volkangokyar01/deck-app/case/v6/v6_ekran_tutucu.png

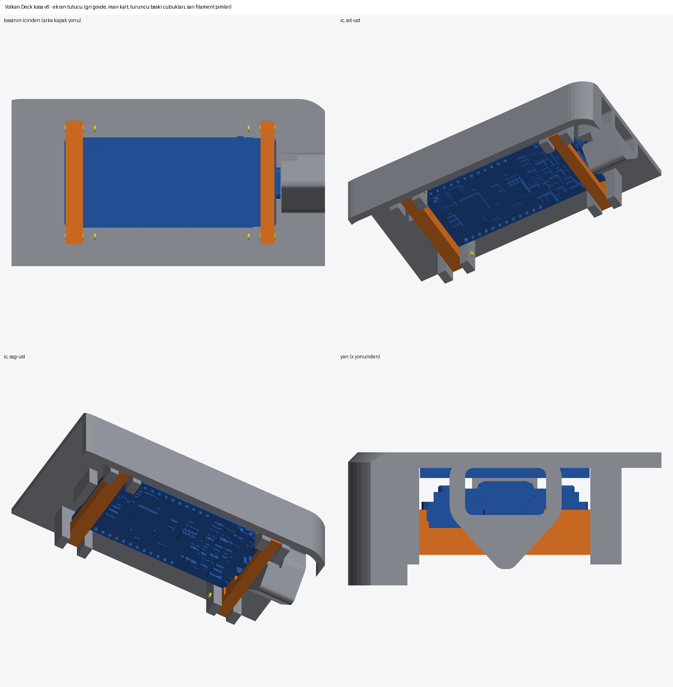
case/v6/v6_ekran_tutucu.png
