volkangokyar01/deck-app/case/v6/v6_usb_ayak.png

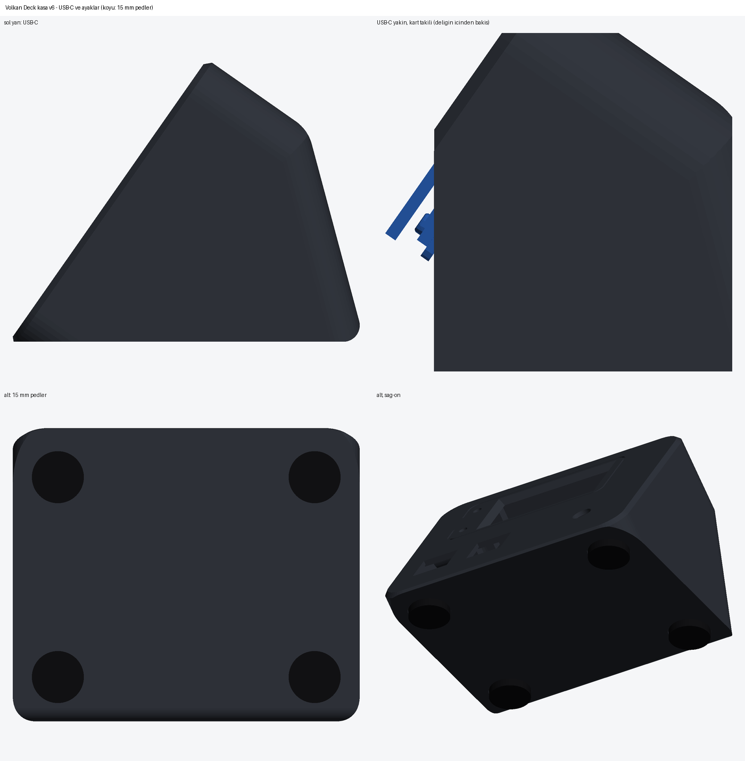
case/v6/v6_usb_ayak.png
