volkangokyar01/deck-app/case/v6/v6_usb_kesit.png

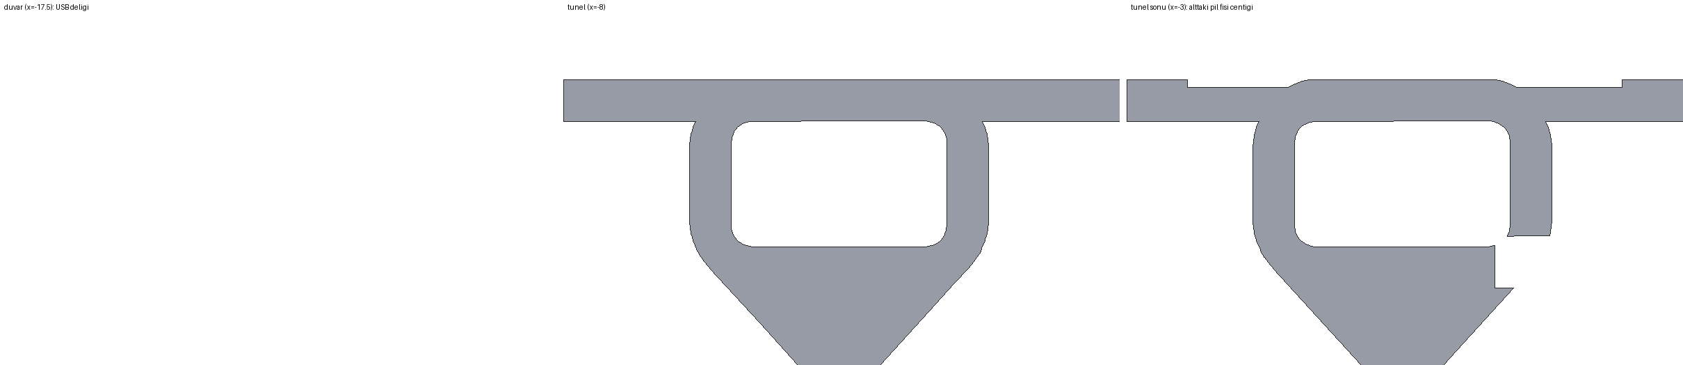
case/v6/v6_usb_kesit.png
