volkangokyar01/deck-app/firmware/VolkanDeck/Proto.h

#pragma once
#include "esp_psram.h"
#include "esp_efuse.h"
#include "esp_efuse_table.h"
#include "mbedtls/base64.h"
#include "esp32-hal-tinyusb.h"

static const size_t LINEBUF_MAX = 128 * 1024;

// Crash breadcrumbs: survive a panic / watchdog reset, reported once in the hello reply ("crash")
RTC_NOINIT_ATTR static uint32_t crumbMagic;
RTC_NOINIT_ATTR static char crumbWhere[28];
static const uint32_t CRUMB_MAGIC = 0x56444352;
static String bootReset, bootCrash;
static void crumbSet(const char* a, const char* b = "") {
  size_t i = 0;
  for (const char* s = a; *s && i < sizeof(crumbWhere) - 1; ) crumbWhere[i++] = *s++;
  if (*b && i < sizeof(crumbWhere) - 1) crumbWhere[i++] = ':';
  for (const char* s = b; *s && i < sizeof(crumbWhere) - 1; ) crumbWhere[i++] = *s++;
  crumbWhere[i] = 0; crumbMagic = CRUMB_MAGIC;
}
static void crumbClear() { crumbMagic = 0; }
static void crumbBoot() {
  esp_reset_reason_t r = esp_reset_reason();
  const char* n = r == ESP_RST_POWERON ? "poweron" : r == ESP_RST_SW ? "software" : r == ESP_RST_PANIC ? "panic" : r == ESP_RST_INT_WDT ? "int_wdt"
                : r == ESP_RST_TASK_WDT ? "task_wdt" : r == ESP_RST_WDT ? "wdt" : r == ESP_RST_BROWNOUT ? "brownout" : r == ESP_RST_DEEPSLEEP ? "deepsleep" : "other";
  bootReset = n;
  bool bad = r == ESP_RST_PANIC || r == ESP_RST_INT_WDT || r == ESP_RST_TASK_WDT || r == ESP_RST_WDT || r == ESP_RST_BROWNOUT;
  crumbWhere[sizeof(crumbWhere) - 1] = 0;
  if (bad) bootCrash = String(n) + (crumbMagic == CRUMB_MAGIC ? String(" @ ") + crumbWhere : String(""));
  crumbMagic = 0;
}
static void ecoSuspend();
static uint32_t transferAt = 0;
static volatile bool usbPartial = false;
static File animUp; static size_t animBytes = 0, animGot = 0; static int animW = 0, animH = 0, animN = 0, animFpsIn = 15; static bool animUpLight = false;
bool configChangedFlag = false;
uint32_t rxBytes = 0, rxLines = 0;
static void* bigAlloc(size_t n) { void* p = psramOk() ? ps_malloc(n) : nullptr; if (!p) p = malloc(n); return p; }      // main applies side effects
String pendingName;
uint32_t companionAt = 0; bool companionNew = false, companionMediaLaunch = false;
bool mediaDirty = false; uint32_t sysLocalAt = 0;
bool mailNew = false;

// Two transports carry the same JSON lines: USB serial and the Bluetooth data channel (Hid.h).
// Replies go back where the command came from; events go to the desktop app's link (USB first).
enum Src : uint8_t { SRC_USB = 0, SRC_BLE };
uint32_t companionUsbAt = 0, companionBleAt = 0;
static int8_t replySrc = -1;                         // set while a command is handled
static bool bleHostOn() { return bleHostConn != BLE_HS_CONN_HANDLE_NONE; }
static bool usbCompanion() { return companionUsbAt && millis() - companionUsbAt < 6000 && Serial; }
static bool bleCompanion() { return companionBleAt && millis() - companionBleAt < 6000 && bleHostOn(); }
static bool companionOn() { return usbCompanion() || bleCompanion(); }
static bool hostListening() { return Serial || bleHostOn(); }   // something may read events
static uint8_t eventSrc() {
  uint16_t act = activeHostConn();               // the computer in use gets the events (1.9.1)
  if (act == HOST_USB && Serial) return SRC_USB;
  if (act != BLE_HS_CONN_HANDLE_NONE && act != HOST_USB) return SRC_BLE;
  return usbCompanion() || (Serial && !bleCompanion()) ? SRC_USB : SRC_BLE;
}
static uint16_t eventConn() {
  uint16_t act = activeHostConn();
  return act != BLE_HS_CONN_HANDLE_NONE && act != HOST_USB ? act : bleHostConn;
}

const char* linkName();

// Bluetooth sending runs on its own task: the main loop (screen, knob) never waits for the radio,
// and the NimBLE host task is never blocked by us, so its buffers keep draining.
// One receive buffer per Bluetooth connection (lines from two computers must never mix)
struct BleLink { volatile uint16_t conn = BLE_HS_CONN_HANDLE_NONE; volatile uint16_t mtu = 23; char* buf = nullptr; size_t have = 0; volatile size_t len = 0; };
static const int BLE_LINKS = 3;
static BleLink bleLinks[BLE_LINKS];
static BleLink* bleLinkOf(uint16_t conn) {
  for (auto& L : bleLinks) if (L.conn == conn) return &L;
  return nullptr;
}
static bool bleConnAlive(uint16_t conn) { return conn != BLE_HS_CONN_HANDLE_NONE && bleLinkOf(conn); }
static uint16_t bleMtuOf(uint16_t conn) { BleLink* L = bleLinkOf(conn); return L ? L->mtu : 23; }
static volatile uint16_t replyConn = BLE_HS_CONN_HANDLE_NONE;   // Bluetooth connection of the command being handled
// wifi_scan waiting for the radio (1.13.6): who asked, so the late reply goes back the same way
struct ScanReq { bool on = false; long id = 0; int8_t src = -1; uint16_t conn = BLE_HS_CONN_HANDLE_NONE; uint32_t at = 0; } scanReq;

struct TxItem { char* p; size_t n; uint16_t conn; };
static QueueHandle_t bleTxQ = nullptr;
static void bleTxTask(void*) {
  TxItem it;
  for (;;) {
    if (xQueueReceive(bleTxQ, &it, portMAX_DELAY) != pdTRUE) continue;
    uint16_t conn = it.conn, mtu = bleMtuOf(conn);
    size_t chunk = mtu > 23 ? min<size_t>(mtu - 3, 244) : 20;
    for (size_t i = 0; i < it.n && bleTx && bleConnAlive(conn); ) {
      size_t k = min(chunk, it.n - i);
      if (bleTx->notify((const uint8_t*)it.p + i, k, conn)) { i += k; continue; }
      int tries = 0;
      while (!bleTx->notify((const uint8_t*)it.p + i, k, conn) && bleConnAlive(conn) && ++tries < 400) vTaskDelay(pdMS_TO_TICKS(5));
      if (tries >= 400) break;                       // link stuck for 2 s: drop the rest of this line
      i += k;
    }
    free(it.p);
  }
}
static void sendJson(JsonDocument& d) {   // replies: always write (host just talked to us)
  uint8_t to = replySrc >= 0 ? replySrc : eventSrc();
  if (to == SRC_USB) { serializeJson(d, Serial); Serial.print('\n'); return; }
  uint16_t conn = replySrc >= 0 ? replyConn : eventConn();
  if (!bleTxQ || !bleConnAlive(conn)) return;
  size_t n = measureJson(d);
  TxItem it; it.p = (char*)bigAlloc(n + 2); if (!it.p) return;
  serializeJson(d, it.p, n + 1); it.p[n] = '\n'; it.n = n + 1; it.conn = conn;
  if (xQueueSend(bleTxQ, &it, 0) != pdTRUE) free(it.p);   // queue full: drop (events are refreshed anyway)
}
static void replyOk(JsonVariantConst id) { JsonDocument r; r["id"] = id; r["ok"] = true; sendJson(r); }
static void replyErr(JsonVariantConst id, const char* e) { JsonDocument r; r["id"] = id; r["ok"] = false; r["error"] = e; sendJson(r); }

static void evtInput(const char* ctl) { if (!hostListening()) return; JsonDocument d; d["evt"] = "input"; d["control"] = ctl; sendJson(d); }
static void evtSelect() {
  if (!hostListening() || items.empty()) return;
  JsonDocument d; d["evt"] = "select";
  // a page opened inside the menu reports its own id (the desktop app feeds media / system pages faster)
  d["app"] = items[sel].kind == K_MENU && subPage ? (subPage == K_MEDIA ? "media" : subPage == K_SYS ? "system" : "connections") : itemId(items[sel]);
  sendJson(d);
}
static void evtStatus() {
  if (!hostListening()) return;
  JsonDocument d; d["evt"] = "status"; d["fw"] = FW_VERSION; d["battery"] = batPct; d["charging"] = charging; d["link"] = linkName();
  d["rx"] = rxBytes; d["lines"] = rxLines; d["psram"] = psramKB();
  d["heap"] = (uint32_t)(ESP.getFreeHeap() / 1024); d["block"] = (uint32_t)(heap_caps_get_largest_free_block(MALLOC_CAP_8BIT) / 1024); sendJson(d);
}
static void evtLaunch(App* a) {
  JsonDocument d; d["evt"] = "launch"; d["app"] = a->id; d["name"] = a->name;
  const Launch& L = a->launch;
  d["method"] = L.method == M_SEARCH ? "search" : L.method == M_TASKBAR ? "taskbar" : L.method == M_KEY ? "key" : "run";
  d["value"] = L.value; if (L.path.length()) d["path"] = L.path; if (L.mac.length()) d["mac"] = L.mac;
  sendJson(d);
}
static void evtMedia(const char* action) {      // play_pause | next | prev | select
  JsonDocument d; d["evt"] = "media"; d["action"] = action; d["player"] = mediaTarget; sendJson(d);
}
static void evtMail(const char* action) {      // open: the user wants the mail app in front
  if (!hostListening()) return;
  JsonDocument d; d["evt"] = "mail"; d["action"] = action; sendJson(d);
}
static void evtSys(const char* key, int value) {  // vol | bright (0..100), mute / micMute (0/1)
  JsonDocument d; d["evt"] = "sys";
  if (!strcmp(key, "mute") || !strcmp(key, "micMute")) d[key] = value != 0; else d[key] = value;
  sendJson(d);
}

static size_t b64decode(const char* src, uint8_t* dst, size_t cap) {
  size_t olen = 0;
  if (mbedtls_base64_decode(dst, cap, &olen, (const unsigned char*)src, strlen(src)) != 0) return 0;
  return olen;
}

static void handleLine(char* buf, size_t len) {
  JsonDocument doc;
  if (deserializeJson(doc, buf, len)) { JsonDocument r; r["ok"] = false; r["error"] = "json"; sendJson(r); return; }
  JsonVariantConst id = doc["id"];
  const char* cmd = doc["cmd"] | "";
  crumbSet("cmd", cmd);
  // Transfers suspend eco without counting desktop traffic as a user touch.
  if (!strcmp(cmd, "set_config") || !strcmp(cmd, "icon_set") || !strncmp(cmd, "anim_", 5) || !strcmp(cmd, "dfu")) { ecoSuspend(); transferAt = millis() | 1; }
  // Two computers at once: the active one feeds the screen (no idle reports: the USB one)
  uint16_t act = activeHostConn(), from = replySrc == SRC_BLE ? replyConn : HOST_USB;
  bool other = act != BLE_HS_CONN_HANDLE_NONE ? from != act : replySrc == SRC_BLE && usbCompanion();
  if (other &&
      (!strcmp(cmd, "stats") || !strcmp(cmd, "media") || !strcmp(cmd, "media_art") || !strcmp(cmd, "sys") || !strcmp(cmd, "mail"))) {
    if (!id.isNull()) replyOk(id);
    return;
  }

  if (!strcmp(cmd, "hello")) {
    JsonDocument r; r["id"] = id; r["ok"] = true; r["fw"] = FW_VERSION; r["name"] = S.name;
    r["battery"] = batPct; r["charging"] = charging; r["link"] = linkName(); r["psram"] = psramKB();
    r["via"] = replySrc == SRC_BLE ? "ble" : "usb"; if (replySrc == SRC_BLE) r["mtu"] = bleMtuOf(replyConn);
    r["anim"] = anim.frames; r["animLight"] = animLight.frames;   // frames stored per theme (0: none)
    r["reset"] = bootReset; if (bootCrash.length()) r["crash"] = bootCrash;
    r["bonds"] = bleBondCount(); r["btOff"] = bt.off; r["wifi"] = wifiStateName();
    // PSRAM diagnosis: does the chip carry PSRAM at all, and did the startup bring it up? Read from the eFuse
    // (PSRAM_CAP 0 none, 1 = 8 MB octal, 2 = 2 MB quad): esp_chip_info never sets CHIP_FEATURE_EMB_PSRAM on the S3
    { uint8_t cap = 0, vendor = 0;
      esp_efuse_read_field_blob(ESP_EFUSE_PSRAM_CAP, &cap, 2); esp_efuse_read_field_blob(ESP_EFUSE_PSRAM_VENDOR, &vendor, 2);
      r["psramCap"] = cap; r["psramVendor"] = vendor; r["embPsram"] = cap != 0;
      r["chipRev"] = ESP.getChipRevision();
      r["psramInit"] = esp_psram_is_initialized(); r["flashMB"] = (uint32_t)(ESP.getFlashChipSize() >> 20); }
    r["heap"] = (uint32_t)(ESP.getFreeHeap() / 1024); r["block"] = (uint32_t)(heap_caps_get_largest_free_block(MALLOC_CAP_8BIT) / 1024);
    sendJson(r);
  }
  else if (!strcmp(cmd, "get_config")) {
    JsonDocument c;
    if (!loadConfigFile(c)) deserializeJson(c, DEFAULT_CONFIG);
    c.remove("sensors");                           // pre-1.4.0 Wi-Fi settings (with the password) are never sent back
    JsonDocument r; r["id"] = id; r["ok"] = true; r["config"] = c; sendJson(r);
  }
  else if (!strcmp(cmd, "set_config")) {
    JsonObject c = doc["config"];
    if (c.isNull() || !c["apps"].is<JsonArray>()) { replyErr(id, "bad_config"); return; }
    c.remove("sensors");                           // old settings pages may still send it; nothing reads it any more
    crumbSet("set_config", "save");
    size_t n = saveConfig(c);
    if (!n) { replyErr(id, "fs"); return; }
    String oldName = S.name;
    crumbSet("set_config", "apply");
    applyConfig(c);
    crumbSet("set_config", "prune");
    pruneIcons();
    crumbSet("set_config", "reply");
    if (S.name != oldName) pendingName = S.name;
    configChangedFlag = true;
    JsonDocument r; r["id"] = id; r["ok"] = true; r["bytes"] = n; sendJson(r);
  }
  else if (!strcmp(cmd, "launch")) {
    Launch L; parseLaunch(doc["launch"], L);
    if (runLaunch(L, L.value)) replyOk(id); else replyErr(id, "no_host");
  }
  else if (!strcmp(cmd, "icon_set")) {              // 1.15.0: 64 x 64 (8192 bytes) or 40 x 40 (3200)
    String aid = (const char*)(doc["app"] | "");
    const char* data = doc["data"] | "";
    uint8_t* tmp = (uint8_t*)bigAlloc(8300);
    if (!tmp) { replyErr(id, "no_mem"); return; }
    size_t n = b64decode(data, tmp, 8300);
    uint8_t side = iconSide(n);
    if (!side || !aid.length()) { free(tmp); replyErr(id, "bad_icon"); return; }
    LittleFS.mkdir("/icons");
    File f = LittleFS.open("/icons/" + aid + ".bin", "w");
    if (!f) { free(tmp); replyErr(id, "fs"); return; }
    f.write(tmp, n); f.close();
    App* a = appById(aid);
    if (a) {
      a->img = true;
      if (a->pix) {                                     // drop the old pixels (size may change)
        bool cached = false;
        for (auto& s : iconSlots) if (s.p == a->pix) { s.a = nullptr; cached = true; }
        if (!cached) free(a->pix);
        a->pix = nullptr;
      }
      a->pixN = side;
      if (psramOk()) { a->pix = (uint16_t*)ps_malloc(n); if (a->pix) memcpy(a->pix, tmp, n); }   // without PSRAM: loaded when drawn
    }
    free(tmp);
    replyOk(id);
  }
  else if (!strcmp(cmd, "anim_begin")) {            // written straight to flash (/anim.tmp), no big RAM buffer needed
    animUpLight = !strcmp(doc["slot"] | "dark", "light");   // 1.7.0: separate animation for the light theme
    animW = doc["w"] | 0; animH = doc["h"] | 0; animN = doc["frames"] | 0; animFpsIn = doc["fps"] | 15;
    size_t bytes = doc["bytes"] | 0;
    if (animW != 128 || animH != 128 || animN < 1 || animN > 60 || bytes != (size_t)animW * animH * 2 * animN) { replyErr(id, "bad_size"); return; }
    if (animUp) animUp.close();
    LittleFS.remove("/anim.tmp");
    animUp = LittleFS.open("/anim.tmp", "w");
    if (!animUp) { replyErr(id, "fs"); return; }
    JsonArrayConst dl = doc["delays"];               // optional per-frame durations (ms), the GIF's own timing
    bool hasDl = dl.size() == (size_t)animN;
    uint8_t hd[12] = { 'V','D','A','N', (uint8_t)animW, (uint8_t)(animW >> 8), (uint8_t)animH, (uint8_t)(animH >> 8), (uint8_t)animN, (uint8_t)(animN >> 8), (uint8_t)animFpsIn, (uint8_t)(hasDl ? 1 : 0) };
    animUp.write(hd, 12);
    if (hasDl) for (JsonVariantConst v : dl) { uint16_t ms = constrain(v.as<int>(), 20, 60000); uint8_t b[2] = { (uint8_t)ms, (uint8_t)(ms >> 8) }; animUp.write(b, 2); }
    animBytes = bytes; animGot = 0;
    replyOk(id);
  }
  else if (!strcmp(cmd, "anim_data")) {
    size_t off = doc["off"] | 0; const char* data = doc["data"] | "";
    if (!animUp) { replyErr(id, "no_begin"); return; }
    if (off != animGot) { replyErr(id, "bad_offset"); return; }
    uint8_t* chunk = (uint8_t*)bigAlloc(8192);       // only while uploading: no permanent 8 KB buffer
    if (!chunk) { replyErr(id, "mem"); return; }
    size_t n = b64decode(data, chunk, 8192);
    if (!n || animGot + n > animBytes) { free(chunk); replyErr(id, "bad_data"); return; }
    bool wrote = animUp.write(chunk, n) == n; free(chunk);
    if (!wrote) { animUp.close(); replyErr(id, "fs_full"); return; }
    animGot += n;
    replyOk(id);
  }
  else if (!strcmp(cmd, "anim_end")) {
    if (!animUp) { replyErr(id, "no_begin"); return; }
    animUp.close();
    if (animGot != animBytes) { LittleFS.remove("/anim.tmp"); replyErr(id, "incomplete"); return; }
    Anim& A = animSlot(animUpLight);
    unloadAnim(A);
    LittleFS.remove(A.path);
    if (!LittleFS.rename("/anim.tmp", A.path)) { replyErr(id, "fs"); return; }
    if (!loadAnim(A)) { replyErr(id, "load"); return; }
    persistAnimChoice(animUpLight ? 0 : animFpsIn);  // the speed setting belongs to the dark slot
    configChangedFlag = true;
    JsonDocument r; r["id"] = id; r["ok"] = true; r["mode"] = A.buf ? "ram" : "flash"; r["slot"] = animUpLight ? "light" : "dark"; sendJson(r);
  }
  else if (!strcmp(cmd, "anim_clear")) {          // remove one slot; the other one is then used for both themes
    Anim& A = animSlot(!strcmp(doc["slot"] | "light", "light"));
    unloadAnim(A); LittleFS.remove(A.path);
    configChangedFlag = true;
    replyOk(id);
  }
  else if (!strcmp(cmd, "companion")) {           // heartbeat from the desktop app (every ~2 s)
    if (!companionOn()) companionNew = true;
    companionMediaLaunch = doc["mediaLaunch"] | false;
    companionAt = millis();
    if (replySrc == SRC_BLE) { companionBleAt = companionAt; bleHostConn = replyConn; } else companionUsbAt = companionAt;
    const char* os = doc["os"] | "";
    if (*os) S.hostMac = !strcmp(os, "mac");
    if (replySrc == SRC_BLE && doc["host"].is<const char*>()) btNameFromConn(replyConn, doc["host"]);
    hostReport(replySrc == SRC_BLE ? replyConn : HOST_USB, doc["idle"] | -1, doc["host"] | "");
    if (doc["ack"] | false) { JsonDocument r; r["id"] = id; r["ok"] = true; r["fw"] = FW_VERSION; sendJson(r); }
  }
  else if (!strcmp(cmd, "stats")) parseStats(doc.as<JsonObjectConst>());   // home-screen widgets, pushed by the desktop app (no reply)
  else if (!strcmp(cmd, "media")) {              // now playing, pushed by the desktop app
    String key = (const char*)(doc["artKey"] | "");
    if (key != media.artKey || media.player != (doc["player"] | "") || media.title != (doc["title"] | "") || media.artist != (doc["artist"] | "")) media.hasArt = false;
    media.artKey = key;
    media.player = (const char*)(doc["player"] | ""); media.name = (const char*)(doc["name"] | "");
    media.title = (const char*)(doc["title"] | ""); media.artist = (const char*)(doc["artist"] | "");
    media.playing = doc["playing"] | false; media.appCtl = !strcmp(doc["ctl"] | "keys", "app");
    media.pos = doc["pos"] | -1.0f; media.dur = doc["dur"] | -1.0f; media.posAt = millis();
    media.stamp = millis() | 1; mediaDirty = true;
  }
  else if (!strcmp(cmd, "media_art")) {
    const char* key = doc["key"] | "";
    if (!*key) { media.hasArt = false; mediaDirty = true; replyOk(id); return; }
    const size_t ART = 64 * 64 * 2;               // decoded straight into the cover buffer (no second 8 KB copy)
    if ((doc["w"] | 0) != 64 || (doc["h"] | 0) != 64) { replyErr(id, "bad_art"); return; }
    if (!media.art) media.art = (uint16_t*)bigAlloc(ART);
    if (!media.art) { replyErr(id, "bad_art"); return; }
    media.hasArt = false;
    if (b64decode(doc["data"] | "", (uint8_t*)media.art, ART) != ART) { mediaDirty = true; replyErr(id, "bad_art"); return; }
    media.artKey = key; media.hasArt = true; mediaDirty = true; replyOk(id);
  }
  else if (!strcmp(cmd, "sys")) {                // volume / brightness, pushed by the desktop app
    uint32_t now = millis();
    JsonVariantConst v = doc["vol"], b = doc["bright"];
    if (now - sysLocalAt > 1500) {               // the user is turning the knob: keep the local value
      sysSt.vol = v.isNull() ? -1 : v.as<int>(); sysSt.bright = b.isNull() ? -1 : b.as<int>();
      sysSt.mute = doc["mute"] | false;
      JsonVariantConst mm = doc["micMute"]; sysSt.mic = mm.isNull() ? -1 : (mm.as<bool>() ? 1 : 0);
    }
    sysSt.stamp = now | 1; mediaDirty = true;
  }
  else if (!strcmp(cmd, "mail")) {               // new mail note, pushed by the desktop app; "ms":0 removes it
    uint32_t ms = constrain(doc["ms"] | 10000, 0, 120000);
    if (!ms) mailNote.until = 0;
    else {
      mailNote.subject = (const char*)(doc["subject"] | "");
      mailNote.unread = doc["unread"] | -1; mailNote.fresh = max(1, doc["new"] | 1);
      mailNote.wrapped = false; mailNote.at = millis(); mailNote.ms = ms; mailNote.until = (mailNote.at + ms) | 1;
      mailNew = true;
    }
    if (!id.isNull()) replyOk(id);
  }
  else if (!strcmp(cmd, "dfu")) {
    if (replySrc == SRC_BLE) { replyErr(id, "usb_only"); return; }
    replyOk(id); Serial.flush(); delay(200);
    usb_persist_restart(RESTART_BOOTLOADER);
  }
  else if (!strcmp(cmd, "ble_forget")) {         // drop every Bluetooth pairing; computers pair again from scratch
    if (replySrc == SRC_BLE) { replyErr(id, "usb_only"); return; }
    if (bleForget()) replyOk(id); else replyErr(id, "busy");
  }
  // Wi-Fi (1.13.0): chosen only in the desktop app; the password is stored on the deck and never sent back
  else if (!strcmp(cmd, "wifi_status")) { JsonDocument r; r["id"] = id; r["ok"] = true; wifiStatusJson(r); sendJson(r); }
  else if (!strcmp(cmd, "wifi_scan")) {             // answered from protoPoll when the scan ends (1.13.6)
    if (scanReq.on) { replyErr(id, "busy"); return; }
    int e = wifiScanStart();
    if (e < 0) { JsonDocument r; r["id"] = id; r["ok"] = false; r["error"] = "scan_failed"; r["heap"] = (uint32_t)(ESP.getFreeHeap() / 1024); sendJson(r); return; }
    scanReq.on = true; scanReq.id = id.as<long>(); scanReq.src = replySrc; scanReq.conn = replyConn; scanReq.at = millis();
  }
  else if (!strcmp(cmd, "wifi_set")) {
    String ssid = (const char*)(doc["ssid"] | ""), pass = (const char*)(doc["pass"] | "");
    if (!ssid.length() || ssid.length() > 32 || pass.length() > 63 || (pass.length() && pass.length() < 8)) { replyErr(id, "invalid"); return; }
    wifiSet(ssid, pass); replyOk(id);
  }
  else if (!strcmp(cmd, "wifi_on")) { wifiSetOn(doc["on"] | true); replyOk(id); }
  else if (!strcmp(cmd, "wifi_forget")) { wifiForget(); replyOk(id); }
  else if (!strcmp(cmd, "restart")) { replyOk(id); delay(200); ESP.restart(); }
  else replyErr(id, "unknown_cmd");
}

struct LineItem { char* p; size_t n; uint8_t src; uint16_t conn; };
static QueueHandle_t lineQ = nullptr;

// Reads USB serial on its own task so drawing the screen never stalls input.

// Line buffers grow only while a long line (config, icon, cover) arrives and shrink back afterwards:
// without PSRAM a permanent 24 KB per buffer left too little heap for "Cihaza yaz".
static const size_t LINEBUF_SMALL = 1024;
static size_t lineCap() { return psramOk() ? LINEBUF_MAX : 24 * 1024; }
static bool lineGrow(char*& buf, size_t& have, size_t need) {
  if (need <= have) return true;
  size_t cap = lineCap(); if (need > cap) return false;
  size_t n = min(cap, max(need, have * 2));
  char* p = psramOk() ? (char*)ps_realloc(buf, n) : nullptr;
  if (!p) p = (char*)realloc(buf, n);             // PSRAM full or not usable: internal RAM
  if (!p) return false;
  buf = p; have = n; return true;
}
// Hand a finished line to the queue without copying it (no second buffer of the same size).
static bool lineTake(char*& buf, size_t& have, size_t len, uint8_t src, uint16_t conn, TickType_t wait) {
  LineItem it; it.n = len; it.src = src; it.conn = conn;
  buf[len] = 0;
  if (have > LINEBUF_SMALL) {
    size_t oldHave = have;
    it.p = buf; buf = nullptr; have = 0;
    if (!lineGrow(buf, have, LINEBUF_SMALL)) { buf = it.p; have = oldHave; return false; }   // keep the old one
  } else {
    it.p = (char*)bigAlloc(len + 1); if (!it.p) return false;
    memcpy(it.p, buf, len + 1);
  }
  if (xQueueSend(lineQ, &it, wait) != pdTRUE) { free(it.p); return false; }
  return true;
}
static void lineShrink(char*& buf, size_t& have) {
  if (have <= LINEBUF_SMALL * 4) return;
  char* p = (char*)realloc(buf, LINEBUF_SMALL); if (p) { buf = p; have = LINEBUF_SMALL; }
}

static void serialTask(void*) {
  size_t have = 0; char* buf = nullptr;
  while (!lineGrow(buf, have, LINEBUF_SMALL)) vTaskDelay(100);
  size_t len = 0;
  for (;;) {
    int n = Serial.available();
    if (n <= 0) { vTaskDelay(1); continue; }
    while (n-- > 0) {
      int c = Serial.read(); if (c < 0) break;
      rxBytes++;
      if (c == '\n') {
        if (len) { rxLines++; lineTake(buf, have, len, SRC_USB, BLE_HS_CONN_HANDLE_NONE, portMAX_DELAY); }
        len = 0; lineShrink(buf, have);
      } else if (c != '\r' && lineGrow(buf, have, len + 2)) buf[len++] = (char)c;
      usbPartial = len != 0;
    }
  }
}

// Bluetooth data channel: called on the NimBLE host task with each written chunk
static void bleRx(uint16_t conn, uint16_t mtu, const uint8_t* p, size_t n) {
  BleLink* L = bleLinkOf(conn);
  if (!L) { L = bleLinkOf(BLE_HS_CONN_HANDLE_NONE); if (!L) return; L->len = 0; L->conn = conn; }
  L->mtu = mtu;
  for (size_t i = 0; i < n; i++) {
    char c = (char)p[i]; rxBytes++;
    if (c == '\n') {
      if (L->len) {
        rxLines++;
        lineTake(L->buf, L->have, L->len, SRC_BLE, conn, 0);   // never block the BLE host task
      }
      L->len = 0; lineShrink(L->buf, L->have);
    } else if (c != '\r' && lineGrow(L->buf, L->have, L->len + 2)) L->buf[L->len++] = c;
  }
}
static void bleDrop(uint16_t conn) {
  BleLink* L = bleLinkOf(conn);
  if (L) { L->len = 0; free(L->buf); L->buf = nullptr; L->have = 0; L->conn = BLE_HS_CONN_HANDLE_NONE; }
}
static bool bleRxPartial() { for (auto& L : bleLinks) if (L.len) return true; return false; }

static void protoBegin() {
  crumbBoot();
  Serial.setRxBufferSize(8192);
  lineQ = xQueueCreate(24, sizeof(LineItem));
  bleTxQ = xQueueCreate(24, sizeof(TxItem));
  xTaskCreatePinnedToCore(bleTxTask, "bletx", 4096, nullptr, 2, nullptr, 0);
  bleRxHook = bleRx; bleDropHook = bleDrop;
  xTaskCreatePinnedToCore(serialTask, "ser", 4096, nullptr, 3, nullptr, 0);
}

static void scanPoll() {
  if (!scanReq.on) return;
  JsonDocument r; r["id"] = scanReq.id;
  int n = wifiScanCollect(r["nets"].to<JsonArray>());
  if (n == WIFI_SCAN_RUNNING) {
    if (millis() - scanReq.at < 12000) return;
    wifiScanAbort();
  }
  scanReq.on = false;
  r["ok"] = n >= 0; if (n < 0) { r["error"] = "scan_failed"; r["heap"] = (uint32_t)(ESP.getFreeHeap() / 1024); }
  replySrc = scanReq.src; replyConn = scanReq.conn; sendJson(r); replySrc = -1; replyConn = BLE_HS_CONN_HANDLE_NONE;
}

static void protoPoll() {
  scanPoll();
  LineItem it;
  while (lineQ && xQueueReceive(lineQ, &it, 0) == pdTRUE) {
    replySrc = it.src; replyConn = it.conn;
    if (it.src == SRC_USB) usbPcSeen = true;                                         // a computer is on the cable
    if (it.src == SRC_BLE && !bleConnAlive(bleHostConn)) bleHostConn = it.conn;   // first app on Bluetooth gets the events
    handleLine(it.p, it.n);
    replySrc = -1; replyConn = BLE_HS_CONN_HANDLE_NONE; free(it.p);
    crumbClear();
  }
}

static bool protoTransferBusy() {
  return animUp || configChangedFlag || usbPartial || bleRxPartial() || (lineQ && uxQueueMessagesWaiting(lineQ)) || (transferAt && millis() - transferAt < 1000);
}
