volkangokyar01/deck-app/firmware/VolkanDeck/Icons.h

#pragma once
#include <stdint.h>
// Line icons (alpha masks), size+4 px square, drawn centred

static const uint8_t ic_game_34[1444] PROGMEM = {0,0,0,0,0,0,0,0,0,0,0,0,0,0,0,0,0,0,0,0,0,0,0,0,0,0,0,0,0,0,0,0,0,0,0,0,0,0,0,0,0,0,0,0,0,0,0,0,0,0,0,0,0,0,0,0,0,0,0,0,0,0,0,0,0,0,0,0,0,0,0,0,0,0,0,0,0,0,0,0,0,0,0,0,0,0,0,0,0,0,0,0,0,0,0,0,0,0,0,0,0,0,0,0,0,0,0,0,0,0,0,0,0,0,0,0,0,0,0,0,0,0,0,0,0,0,0,0,0,0,0,0,0,0,0,0,0,0,0,0,0,0,0,0,0,0,0,0,0,0,0,0,0,0,0,0,0,0,0,0,0,0,0,0,0,0,0,0,0,0,0,0,0,0,0,0,0,0,0,0,0,0,0,0,0,0,0,0,0,0,0,0,0,0,0,0,0,0,0,0,0,0,0,0,0,0,0,0,0,0,0,0,0,0,0,0,0,0,0,0,0,0,0,0,0,0,0,0,0,0,0,0,0,0,0,0,0,0,0,0,0,0,0,0,0,0,0,0,0,0,0,0,0,0,0,0,0,0,0,0,0,0,0,0,0,0,0,0,0,0,0,0,0,0,0,0,0,0,0,0,0,0,0,0,0,0,0,0,0,0,0,0,0,0,0,0,0,0,0,0,0,0,0,0,0,0,0,0,0,0,0,0,0,0,0,0,0,0,0,0,0,0,0,0,0,0,0,0,0,0,0,0,0,0,0,0,0,0,0,0,0,0,0,0,0,0,0,0,0,0,0,0,0,0,0,0,0,0,0,0,0,0,0,0,0,0,0,0,0,0,0,0,0,0,0,0,0,0,0,0,0,0,0,0,0,0,0,0,0,0,0,0,0,0,0,0,0,0,0,0,0,0,0,0,0,0,0,0,0,0,0,0,0,0,0,0,0,0,0,0,0,0,0,0,0,0,0,0,4,48,64,64,64,64,64,64,64,64,64,64,64,64,64,64,48,3,0,0,0,0,0,0,0,0,0,0,0,0,0,0,0,0,0,0,71,205,251,255,255,255,255,255,255,255,255,255,255,255,255,255,255,255,255,251,205,68,0,0,0,0,0,0,0,0,0,0,0,0,0,0,3,135,254,255,255,255,255,255,255,255,255,255,255,255,255,255,255,255,255,255,255,255,255,253,131,3,0,0,0,0,0,0,0,0,0,0,0,0,136,255,255,255,255,255,255,255,255,255,255,255,255,255,255,255,255,255,255,255,255,255,255,255,255,135,0,0,0,0,0,0,0,0,0,0,0,58,255,255,255,152,64,206,255,236,1,0,0,0,0,0,0,0,0,0,0,0,13,52,157,255,255,254,55,0,0,0,0,0,0,0,0,0,0,176,255,255,130,0,0,235,255,255,42,0,0,0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
static const uint8_t ic_globe_11[225] PROGMEM = {0,0,0,0,0,0,0,0,0,0,0,0,0,0,0,0,0,0,0,0,0,0,0,0,0,0,0,0,0,0,0,0,0,0,0,1,29,102,28,1,0,0,0,0,0,0,0,0,0,23,202,255,255,255,201,22,0,0,0,0,0,0,0,14,223,162,193,239,191,166,221,13,0,0,0,0,0,0,158,157,0,214,95,207,0,158,153,0,0,0,0,0,0,243,23,0,239,34,235,0,23,237,0,0,0,0,0,22,255,255,255,255,255,255,255,255,255,17,0,0,0,0,0,244,11,0,238,33,236,0,10,240,0,0,0,0,0,0,158,137,0,212,82,208,0,138,152,0,0,0,0,0,0,15,223,165,188,229,185,165,221,13,0,0,0,0,0,0,0,14,152,245,255,245,150,13,0,0,0,0,0,0,0,0,0,0,4,49,4,0,0,0,0,0,0,0,0,0,0,0,0,0,0,0,0,0,0,0,0,0,0,0,0,0,0,0,0,0,0,0,0,0,0,0,0};
static const uint8_t ic_record_34[1444] PROGMEM = {0,0,0,0,0,0,0,0,0,0,0,0,0,0,0,0,0,0,0,0,0,0,0,0,0,0,0,0,0,0,0,0,0,0,0,0,0,0,0,0,0,0,0,0,0,0,0,0,0,0,0,0,0,0,0,0,0,0,0,0,0,0,0,0,0,0,0,0,0,0,0,0,0,0,0,0,0,0,0,0,0,0,0,0,0,0,0,0,0,0,0,0,0,0,0,0,0,0,0,0,0,0,0,0,0,0,0,0,0,0,0,0,0,0,0,0,0,0,0,0,0,0,0,0,0,0,0,0,0,0,0,0,0,0,0,0,0,0,0,0,0,0,0,0,0,0,0,0,0,0,0,0,0,0,0,0,0,0,0,0,0,0,0,0,0,0,0,0,0,0,0,0,0,0,0,0,0,0,0,0,0,0,0,0,0,0,0,0,0,0,0,0,0,0,0,0,0,0,0,0,0,0,0,0,0,0,0,0,0,0,0,0,0,0,0,0,0,0,0,0,0,0,0,0,0,0,0,0,0,0,0,0,0,0,0,0,0,0,0,0,0,0,35,117,189,219,244,244,219,188,117,32,0,0,0,0,0,0,0,0,0,0,0,0,0,0,0,0,0,0,0,0,0,0,0,0,0,0,74,192,255,255,255,255,255,255,255,255,255,255,190,73,0,0,0,0,0,0,0,0,0,0,0,0,0,0,0,0,0,0,0,0,0,0,2,164,255,255,255,255,255,255,255,255,255,255,255,255,255,255,157,1,0,0,0,0,0,0,0,0,0,0,0,0,0,0,0,0,0,0,0,2,161,255,255,255,255,242,192,139,88,88,140,192,242,255,255,255,255,156,1,0,0,0,0,0,0,0,0,0,0,0,0,0,0,0,0,0,0,135,255,255,255,247,119,3,0,0,0,0,0,0,5,120,249,255,255,255,132,0,0,0,0,0,0,0,0,0,0,0,0,0,0,0,0,0,85,255,255,255,190,31,0,0,0,0,0,0,0,0,0,0,34,194,255,255,255,87,0,0,0,0,0,0,0,0,0,0,0,0,0,0,0,21,245,255,255,191,0,0,0,0,0,0,0,0,0,0,0,0,0,0,196,255,255,244,18,0,0,0,0,0,0,0,0,0,0,0,0,0,0,152,255,255,242,28,0,0,0,0,28,107,164,164,106,26,0,0,0,0,28,243,255,255,147,0,0,0,0,0,0,0,0,0,0,0,0,0,13,249,255,255,96,0,0,0,0,104,242,255,255,255,255,241,99,0,0,0,0,100,255,255,249,9,0,0,0,0,0,0,0,0,0,0,0,0,88,255,255,241,0,0,0,0,110,255,255,255,255,255,255,255,255,108,0,0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
static const uint8_t ic_terminal_11[225] PROGMEM = {0,0,0,0,0,0,0,0,0,0,0,0,0,0,0,0,0,0,0,0,0,0,0,0,0,0,0,0,0,0,0,0,0,0,0,0,0,0,0,0,0,0,0,0,0,0,0,0,23,64,64,64,64,64,64,64,22,0,0,0,0,0,0,168,213,192,192,192,192,192,213,165,0,0,0,0,0,0,172,101,65,0,0,0,0,85,169,0,0,0,0,0,0,172,118,236,67,0,0,0,86,170,0,0,0,0,0,0,172,84,69,227,2,0,0,84,168,0,0,0,0,0,0,172,118,234,68,167,192,190,114,168,0,0,0,0,0,0,172,99,73,0,122,128,128,113,169,0,0,0,0,0,0,170,213,192,192,192,192,192,213,167,0,0,0,0,0,0,37,64,64,64,64,64,64,64,36,0,0,0,0,0,0,0,0,0,0,0,0,0,0,0,0,0,0,0,0,0,0,0,0,0,0,0,0,0,0,0,0,0,0,0,0,0,0,0,0,0,0,0,0,0,0,0,0};
static const uint8_t ic_calc_34[1444] PROGMEM = {0,0,0,0,0,0,0,0,0,0,0,0,0,0,0,0,0,0,0,0,0,0,0,0,0,0,0,0,0,0,0,0,0,0,0,0,0,0,0,0,0,0,0,0,0,0,0,0,0,0,0,0,0,0,0,0,0,0,0,0,0,0,0,0,0,0,0,0,0,0,0,0,0,0,0,0,0,0,0,0,0,0,0,0,0,0,0,0,0,0,0,0,0,0,0,0,0,0,0,0,0,0,0,0,0,0,0,0,0,0,0,0,0,0,0,0,0,0,0,0,0,0,0,0,0,0,0,0,0,0,0,0,0,0,0,0,0,0,0,0,0,0,0,0,0,0,0,0,0,0,0,0,0,0,0,0,0,0,0,0,0,0,51,64,64,64,64,64,64,64,64,64,64,64,64,64,64,64,64,51,0,0,0,0,0,0,0,0,0,0,0,0,0,0,0,0,0,0,0,181,255,255,255,255,255,255,255,255,255,255,255,255,255,255,255,255,255,255,177,0,0,0,0,0,0,0,0,0,0,0,0,0,0,0,0,0,11,255,255,255,255,255,255,255,255,255,255,255,255,255,255,255,255,255,255,255,255,10,0,0,0,0,0,0,0,0,0,0,0,0,0,0,0,0,13,255,255,255,195,192,192,192,192,192,192,192,192,192,192,192,192,195,255,255,255,13,0,0,0,0,0,0,0,0,0,0,0,0,0,0,0,0,15,255,255,255,14,0,0,0,0,0,0,0,0,0,0,0,0,15,255,255,255,14,0,0,0,0,0,0,0,0,0,0,0,0,0,0,0,0,15,255,255,255,14,0,0,0,0,0,0,0,0,0,0,0,0,15,255,255,255,14,0,0,0,0,0,0,0,0,0,0,0,0,0,0,0,0,13,255,255,255,13,37,163,192,192,192,192,192,192,192,192,163,36,13,255,255,255,13,0,0,0,0,0,0,0,0,0,0,0,0,0,0,0,0,15,255,255,255,14,168,255,255,255,255,255,255,255,255,255,255,163,15,255,255,255,14,0,0,0,0,0,0,0,0,0,0,0,0,0,0,0,0,14,255,255,255,13,168,255,255,255,255,255,255,255,255,255,255,166,15,255,255,255,14,0,0,0,0,0,0,0,0,0,0,0,0,0,0,0,0,13,255,255,255,13,33,116,128,128,128,128,128,128,128,128,115,32,13,255,255,255,13,0,0,0,0,0,0,0,0,0,0,0,0,0,0,0,0,15,255,255,255,14,0,0,0,0,0,0,0,0,0,0,0,0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
static const uint8_t ic_calc_11[225] PROGMEM = {0,0,0,0,0,0,0,0,0,0,0,0,0,0,0,0,0,0,0,0,0,0,0,0,0,0,0,0,0,0,0,0,0,0,28,64,64,64,64,64,28,0,0,0,0,0,0,0,0,187,255,255,255,255,255,184,0,0,0,0,0,0,0,0,193,69,63,64,63,70,192,0,0,0,0,0,0,0,0,193,126,192,192,192,124,192,0,0,0,0,0,0,0,0,193,90,56,84,58,90,192,0,0,0,0,0,0,0,0,194,105,72,117,73,106,192,0,0,0,0,0,0,0,0,193,111,92,144,95,110,192,0,0,0,0,0,0,0,0,194,105,72,117,73,106,192,0,0,0,0,0,0,0,0,194,65,0,0,0,66,193,0,0,0,0,0,0,0,0,191,255,255,255,255,255,190,0,0,0,0,0,0,0,0,42,64,64,64,64,64,41,0,0,0,0,0,0,0,0,0,0,0,0,0,0,0,0,0,0,0,0,0,0,0,0,0,0,0,0,0,0,0,0,0,0};
static const uint8_t ic_activity_34[1444] PROGMEM = {0,0,0,0,0,0,0,0,0,0,0,0,0,0,0,0,0,0,0,0,0,0,0,0,0,0,0,0,0,0,0,0,0,0,0,0,0,0,0,0,0,0,0,0,0,0,0,0,0,0,0,0,0,0,0,0,0,0,0,0,0,0,0,0,0,0,0,0,0,0,0,0,0,0,0,0,0,0,0,0,0,0,0,0,0,0,0,0,0,0,0,0,0,0,0,0,0,0,0,0,0,0,0,0,0,0,0,0,0,0,0,0,0,0,0,0,0,0,0,0,0,0,0,0,0,0,0,0,0,0,0,0,0,0,0,0,0,0,0,0,0,0,0,0,0,0,0,0,0,0,0,0,0,0,0,0,0,0,0,0,0,0,0,0,0,0,0,0,0,0,0,0,0,0,0,0,0,0,0,0,0,0,0,0,0,0,0,0,0,0,0,0,0,0,0,0,0,0,0,0,0,0,0,0,0,0,0,0,0,0,0,0,0,0,0,0,0,0,0,0,0,0,0,0,0,0,0,0,0,0,0,0,0,0,0,0,0,0,0,0,0,0,0,0,0,0,0,0,0,0,0,0,0,0,0,0,0,0,0,0,0,0,0,0,0,0,0,0,0,0,0,0,0,0,0,0,0,0,0,0,0,77,81,0,0,0,0,0,0,0,0,0,0,0,0,0,0,0,0,0,0,0,0,0,0,0,0,0,0,0,0,0,0,0,0,0,0,0,59,255,255,118,0,0,0,0,0,0,0,0,0,0,0,0,0,0,0,0,0,0,0,0,0,0,0,0,0,0,0,0,0,0,0,0,0,0,176,255,255,224,0,0,0,0,0,0,0,0,0,0,0,0,0,0,0,0,0,0,0,0,0,0,0,0,0,0,0,0,0,0,0,0,0,29,254,255,255,255,42,0,0,0,0,0,0,0,0,0,0,0,0,0,0,0,0,0,0,0,0,0,0,0,0,0,0,0,0,0,0,0,0,139,255,255,255,255,115,0,0,0,0,0,0,0,0,0,0,0,0,0,0,0,0,0,0,0,0,0,0,0,0,0,0,0,0,0,0,0,7,241,255,255,255,255,188,0,0,0,0,0,0,0,0,0,0,0,0,0,0,0,0,0,0,0,0,0,0,0,0,0,0,0,0,0,0,0,99,255,255,248,255,255,250,11,0,0,0,0,0,0,0,0,0,0,0,0,0,0,0,0,0,0,0,0,0,0,0,0,0,0,0,0,0,0,213,255,255,133,234,255,255,78,0,0,0,0,0,0,0,0,0,0,0,0,0,0,0,0,0,0,0,0,0,0,0,0,0,0,0,0,0,62,255,255,251,23,157,255,255,152,0,0,0,0,0,0,0,0,0,0,0,0,0,0,0,0,0,0,0,0,0,0,0,0,0,0,0,0,0,171,255,255,167,0,83,255,255,228,0,0,0,0,0,0,0,0,0,0,0,0,0,0,0,0,0,0,0,0,0,0,0,45,125,128,128,128,130,254,255,255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
struct LineIcon{const char* id; const uint8_t* a34; const uint8_t* a21; const uint8_t* a11;};
static const LineIcon LINE_ICONS[] = {{"game",ic_game_34,ic_game_21,ic_game_11},{"chat",ic_chat_34,ic_chat_21,ic_chat_11},{"music",ic_music_34,ic_music_21,ic_music_11},{"globe",ic_globe_34,ic_globe_21,ic_globe_11},{"record",ic_record_34,ic_record_21,ic_record_11},{"folder",ic_folder_34,ic_folder_21,ic_folder_11},{"gear",ic_gear_34,ic_gear_21,ic_gear_11},{"terminal",ic_terminal_34,ic_terminal_21,ic_terminal_11},{"calc",ic_calc_34,ic_calc_21,ic_calc_11},{"activity",ic_activity_34,ic_activity_21,ic_activity_11},{"mail",ic_mail_34,ic_mail_21,ic_mail_11},{"code",ic_code_34,ic_code_21,ic_code_11},{"star",ic_star_34,ic_star_21,ic_star_11},{"home",ic_home_34,ic_home_21,ic_home_11}};
static const int LINE_ICON_COUNT = 14;
